FoxVK/DFMT/diploma/figures/breadborad-landscape.jpg

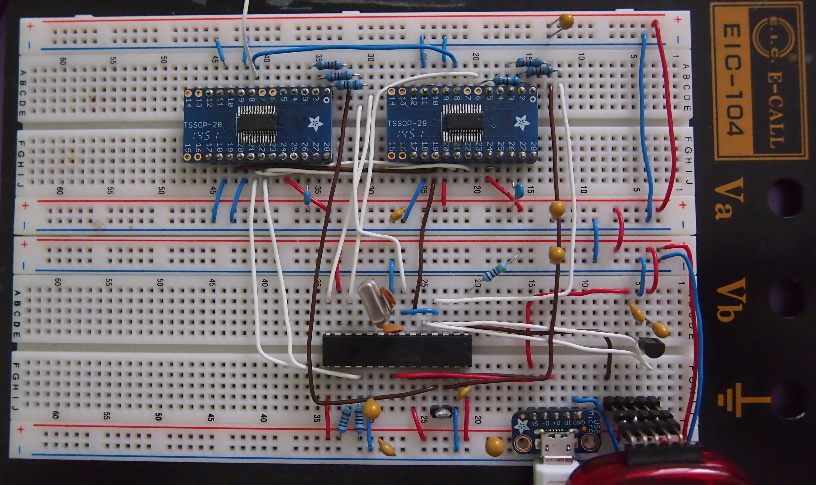
diploma/figures/breadborad-landscape.jpg
