FoxVK/DFMT/diploma/figures/breadborad-portrait.jpg

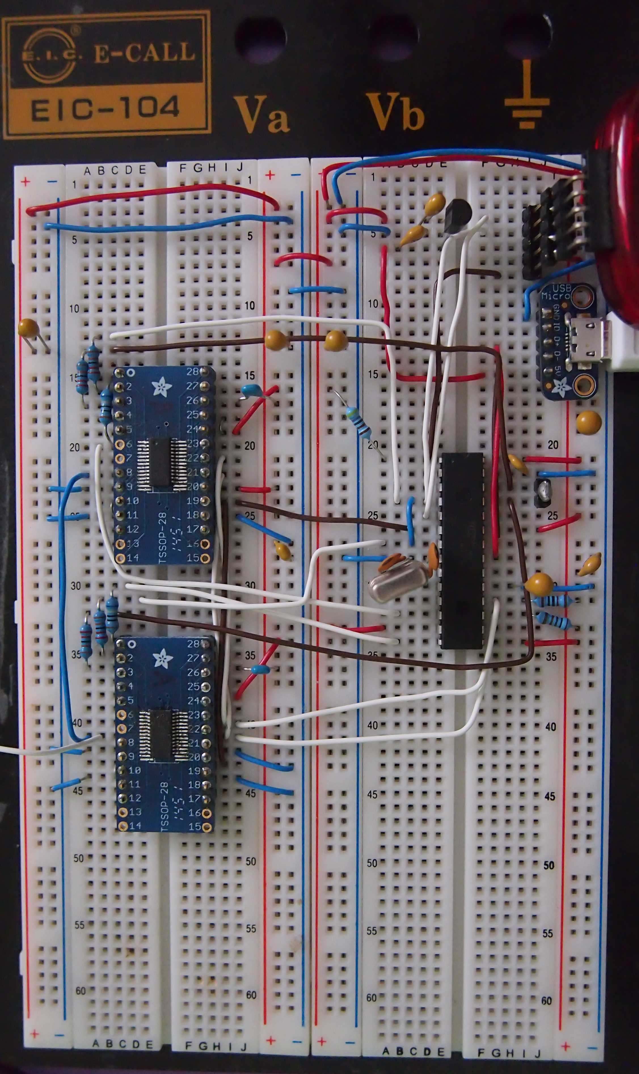
diploma/figures/breadborad-portrait.jpg
