FoxVK/DFMT/diploma/figures/dfmt-win-no-drv.png

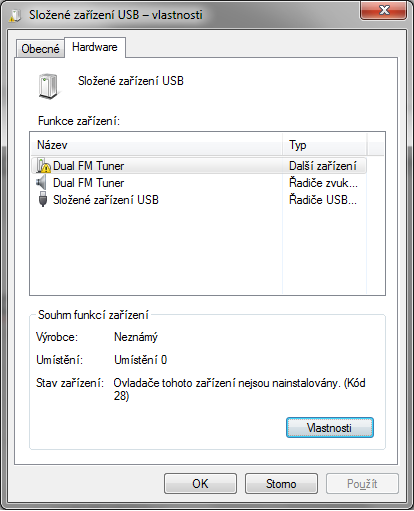
diploma/figures/dfmt-win-no-drv.png
