FoxVK/DFMT/diploma/figures/gui.png

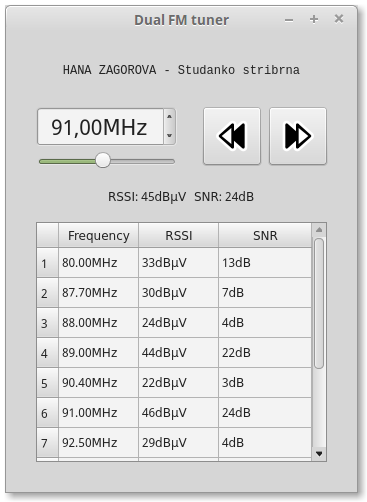
diploma/figures/gui.png
