FoxVK/DFMT/diploma/figures/i2s_format.png

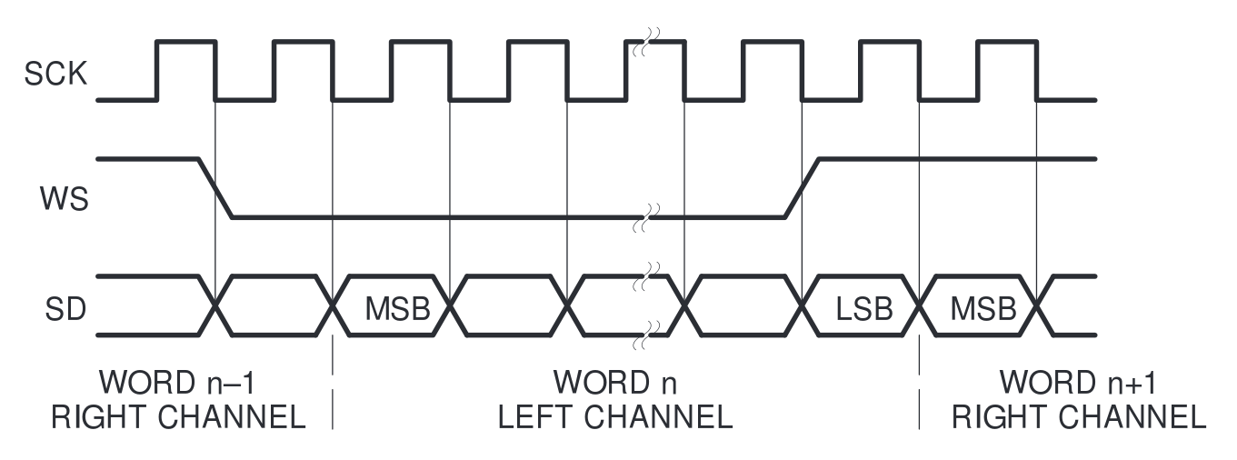
diploma/figures/i2s_format.png
