FoxVK/DFMT/diploma/figures/prohlaseni.jpg

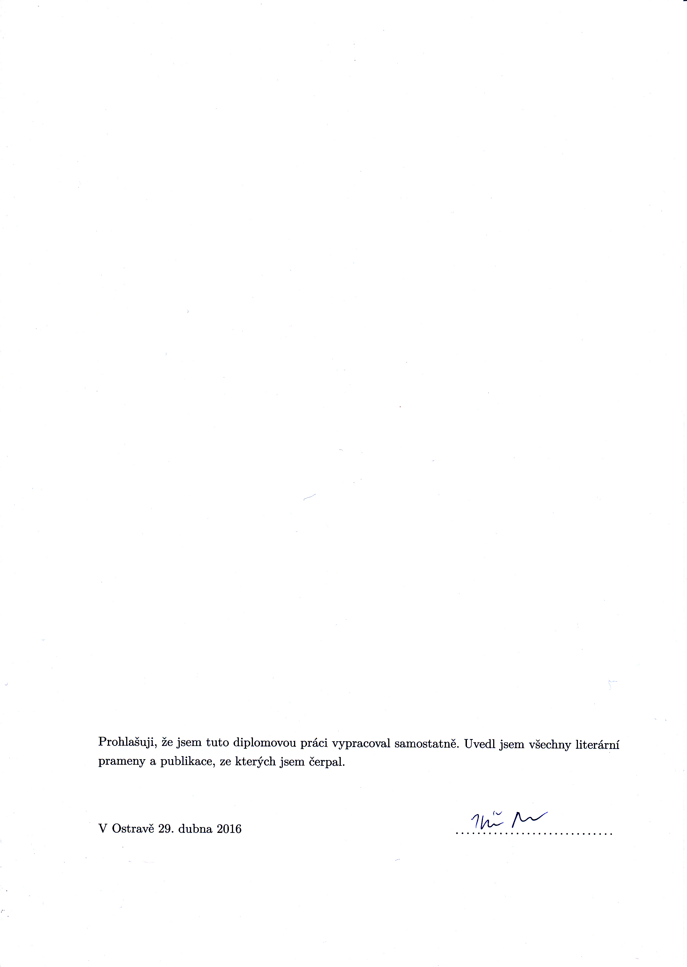
diploma/figures/prohlaseni.jpg
