FoxVK/DFMT/diploma/figures/usb-bdt-hwsw.png

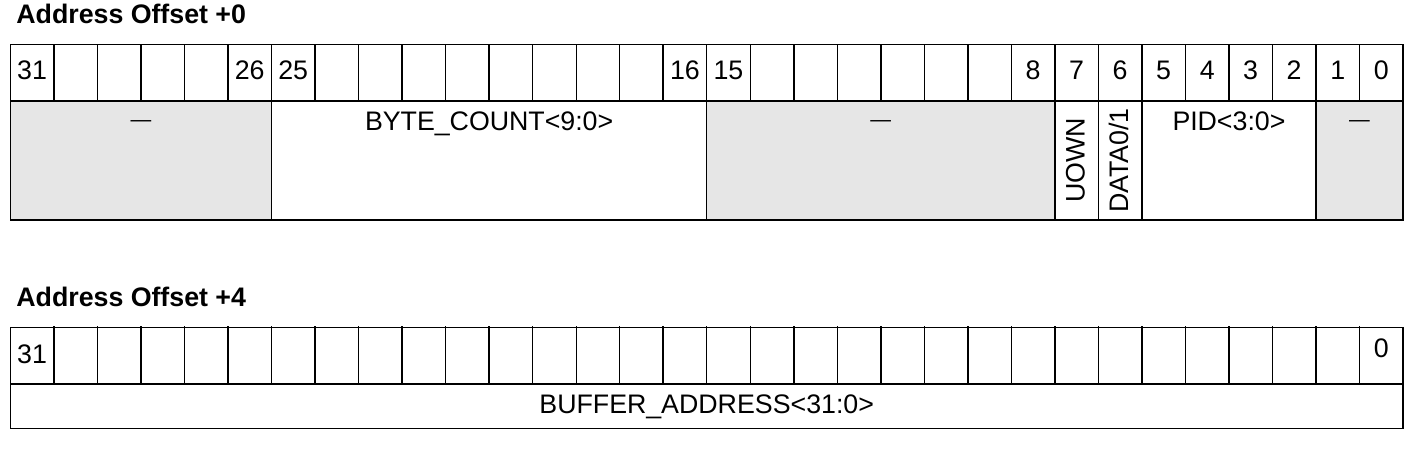
diploma/figures/usb-bdt-hwsw.png
