FoxVK/DFMT/diploma/figures/usb-bdt-swhw.png

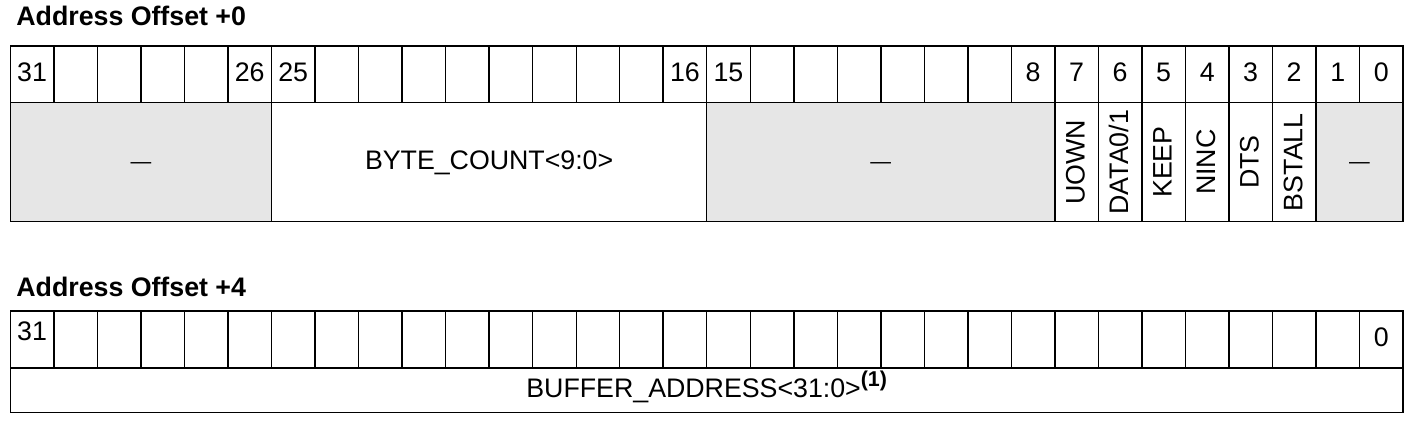
diploma/figures/usb-bdt-swhw.png
