FoxVK/DFMT/media/boardV1-botom.jpg

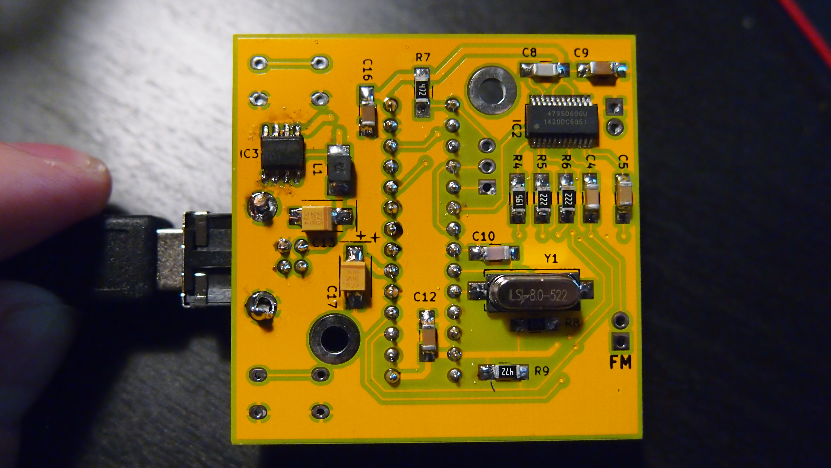
media/boardV1-botom.jpg
