FoxVK/DFMT/media/gui.png

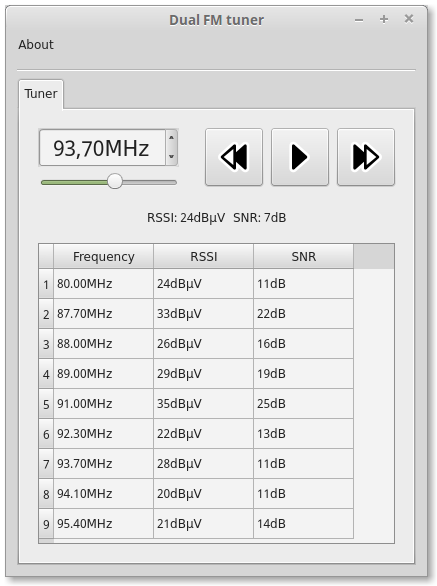
media/gui.png
