FoxVK/DFMT/firmware/tuner_audio.c

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
    Copyright: Pavel Kovar 2015 <pavel.kovar@vsetin.org>.
 */
// </editor-fold>

#include <xc.h>
#include "drv/utils.h"
#include "tuner_audio.h"
#include "drv/debug_uart.h"


static struct{
    Queue free, filled;
    void *qbuf_free[AUDIO_PACKET_BUFS], *qbuf_filled[AUDIO_PACKET_BUFS];
    AudioFrame  frame_buf[AUDIO_PACKET_BUFS];
}aud_data[2];

static struct SampleRateCorrection{
    enum {SR_COR_OFF, SR_COR_FIRST_RUN, SR_COR_ON} state;  ///< OFF = suspended
    int direciton;   ///<  +1 one more or -1 one less
    unsigned cor_rate;  ///<How often
    unsigned cor_cntr;
    int last_dif;  ///< tuner packet - usb sofs from last time
    
    int tuner_samples;
    int usb_sofs;
}sr_cor;

static volatile unsigned int *DCHxDSA[] = {&DCH0DSA, &DCH1DSA, &DCH2DSA, &DCH3DSA};
static volatile unsigned int *DCHxDSIZ[] = {&DCH0DSIZ, &DCH1DSIZ, &DCH2DSIZ, &DCH3DSIZ};    
static volatile __DCH0CONbits_t *DCHxCONbits[] = {&DCH0CONbits, 
                                    (__DCH0CONbits_t*)&DCH1CONbits, 
                                    (__DCH0CONbits_t*)&DCH2CONbits, 
                                    (__DCH0CONbits_t*)&DCH3CONbits};
static volatile __DCH0INTbits_t *DCHxINTbits[] = {&DCH0INTbits, 
                                    (__DCH0INTbits_t*)&DCH1INTbits, 
                                    (__DCH0INTbits_t*)&DCH2INTbits, 
                                    (__DCH0INTbits_t*)&DCH3INTbits};

static size_t sr_cor_packet_size(int tuner);
static void sr_cor_init();

static void arm_dma(int dma)
{
    static char *title[] = {"AD0\r\n","AD1\r\n","AD2\r\n","AD3\r\n"};
    static char *num[] = {"0 ","1 ","2 ","3 ","4 ", "5 ", "6 ", "7 ", "8 ", "9 ", "10 "};
    
    
    int tuner = (dma>1) ? 1 : 0 ;
    
    void *buf = queue_pop(&aud_data[tuner].free);
    if(!buf)
    {
        buf = queue_pop(&aud_data[tuner].filled);
    }
    if(!buf)    
        debughalt();
    size_t size = sr_cor_packet_size(tuner);  
    
    ((AudioFrame*)buf)->size = (size>(AUDIO_SAMPLE_RATE * AUDIO_SAMPLE_CHAN_BYTES * 2)) ? (AUDIO_SAMPLE_RATE * AUDIO_SAMPLE_CHAN_BYTES * 2) : size;
    
    *DCHxDSA[dma]  = virt2phy(buf);
    *DCHxDSIZ[dma] = size;
    

}

static void dma_init()
{
    DCH0SSA = DCH1SSA = virt2phy((void*)&SPI1BUF);
    DCH2SSA = DCH3SSA = virt2phy((void*)&SPI2BUF);
    
    DCH0SSIZ = DCH1SSIZ = DCH2SSIZ = DCH3SSIZ = AUDIO_SAMPLE_CHAN_BYTES;
    DCH0CSIZ = DCH1CSIZ = DCH2CSIZ = DCH3CSIZ = AUDIO_SAMPLE_CHAN_BYTES; //bytes per event
    
    DCH0DSIZ = DCH1DSIZ = DCH2DSIZ = DCH3DSIZ = sizeof(AudioFrame);
    
    DCH0CONbits.CHCHN = DCH1CONbits.CHCHN = 1;
    DCH2CONbits.CHCHN = DCH3CONbits.CHCHN = 1;
    //CHCHNS=1 Chain to channel lower in natural priority (CH1 will be enabled by CH2 transfer complete)
    DCH0CONbits.CHCHNS = DCH2CONbits.CHCHNS = 1;
    
    DCH0ECONbits.CHSIRQ = DCH1ECONbits.CHSIRQ = 37;   //cell start interrupt number 
    DCH0ECONbits.SIRQEN = DCH1ECONbits.SIRQEN = 1;    //start cell transfer when chsirq match
    
    DCH2ECONbits.CHSIRQ = DCH3ECONbits.CHSIRQ = 51;   //cell start interrupt number 
    DCH2ECONbits.SIRQEN = DCH3ECONbits.SIRQEN = 1;    //start cell transfer when chsirq match
    
    
    DCH0INT = DCH1INT = DCH2INT = DCH3INT = 0;
    
    
    int i;
    for(i=0; i<4; i++)
        arm_dma(i);    
    
    DCH0INTbits.CHDDIF = DCH1INTbits.CHDDIF = 0;
    DCH2INTbits.CHDDIF = DCH3INTbits.CHDDIF = 0;
    DCH0CONbits.CHEN = 1;
    DCH2CONbits.CHEN = 1;
}

static void i2s_init()
{
    SPI1CONbits.ON = SPI2CONbits.ON = 0;
    Nop();
    SPI1CONbits.DISSDO = SPI2CONbits.DISSDO = 1;     //disable output bit
    //SPI1CONbits.ENHBUF = 1;     //enchanced buffer enable
    SPI1CONbits.MSTEN = 1;      //enable master - we will generate clock on I2S1 not on I2S2!
    SPI1CON2bits.AUDEN = SPI2CON2bits.AUDEN = 1;     //enable audio

    SPI1CONbits.CKP = SPI2CONbits.CKP = 1;        //clock idle in low

    SPI1STATbits.SPIROV = SPI2STATbits.SPIROV = 0;    //no overflow
    
    SPI1BRG = 12;       //clock,  32bit frame X 48khz sampling = 1536kHz - now we have 1?538?461,538461538
    
    IFS1bits.SPI1RXIF = 0;
    IFS1bits.SPI2RXIF = 0;
}

void* tuner_audio_get_buf(int tuner)
{
    if (queue_count(&aud_data[tuner].filled) <= 1)
    {
        return NULL;
    }
    else
        return queue_pop(&aud_data[tuner].filled);
}

bool  tuner_audio_put_buf(int tuner, void* buf)
{
    if (queue_full(&aud_data[tuner].free))
        return false;
    else
    {
        queue_push(&aud_data[tuner].free, buf);
        return true;
    }
}



void tuner_audio_init()
{
    int i,j;
    for(i=0; i<2; i++)
    {
        queue_init(&aud_data[i].filled, aud_data[i].qbuf_filled, AUDIO_PACKET_BUFS);
        queue_init(&aud_data[i].free,   aud_data[i].qbuf_free,   AUDIO_PACKET_BUFS);
        
        for (j=0; j<AUDIO_PACKET_BUFS; j++)
            queue_push(&aud_data[i].free, &aud_data[i].frame_buf[j]);
    }
       
    dma_init();
    i2s_init();
    sr_cor_init();
    DMACONbits.ON = 1;
    SPI2CONbits.ON = 1;
    SPI1CONbits.ON = 1;
}

void tuner_audio_task()
{
    int i = 0;
    for (;i<4;i++)
    {
        if(DCHxINTbits[i]->CHDDIF)
        {
            DCHxINTbits[i]->CHDDIF = 0;
            queue_push(&aud_data[(i>1)?1:0].filled, phy2virt(*DCHxDSA[i]));
            arm_dma(i);
        }
    }
}

void tuner_audio_sof()
{
    sr_cor.usb_sofs++;
    
    if( sr_cor.state == SR_COR_FIRST_RUN && 
        sr_cor.tuner_samples > 50 &&
        sr_cor.usb_sofs > 50)
    {
        sr_cor.state = SR_COR_ON;
        sr_cor.tuner_samples = sr_cor.usb_sofs = 0;
    }
    
    if(sr_cor.usb_sofs == AUDIO_SR_SOFS_INTERVAL && sr_cor.state == SR_COR_ON)
    {
        int dif = (sr_cor.tuner_samples - sr_cor.usb_sofs) ;
        dif += sr_cor.last_dif;
        sr_cor.last_dif = dif;

        if(dif == 0)
        {
            sr_cor.direciton = 0;
        }
        else
        {            
            int rate = (AUDIO_SR_SOFS_INTERVAL / AUDIO_SAMPLE_RATE) / dif;

            if(rate < 0)
            {
                sr_cor.cor_rate = (0 - rate);
                sr_cor.direciton = -1;
            }
            else if(rate == 0)
            {
                sr_cor.direciton = 0;
                sr_cor.last_dif = 0;
            }
            else
            {
                sr_cor.cor_rate = rate;
                sr_cor.direciton = 1;
            }
        }

        sr_cor.tuner_samples = sr_cor.usb_sofs = 0;
    }
}

static size_t sr_cor_packet_size(int tuner)
{
    if(tuner==0)
    {
        if(sr_cor.state!=SR_COR_OFF)
            sr_cor.tuner_samples++;
        
        sr_cor.cor_cntr++;
        if(sr_cor.cor_cntr >= sr_cor.cor_rate)
            sr_cor.cor_cntr = 0;
    }
    
    if(sr_cor.cor_cntr != 1)
        return (AUDIO_SAMPLE_RATE * AUDIO_SAMPLE_CHAN_BYTES * 2 );
    else
        return (AUDIO_SAMPLE_RATE * AUDIO_SAMPLE_CHAN_BYTES * 2 )+ sr_cor.direciton;
}

static void sr_cor_init()
{
        sr_cor.cor_rate = 0;
        sr_cor.direciton = 0;
        sr_cor.tuner_samples = 0;
        sr_cor.usb_sofs = 0;
        sr_cor.last_dif = 0;
        sr_cor.state = SR_COR_OFF;
        sr_cor.cor_cntr = 0;
}

void tuner_audio_sr_cor_on(bool state)
{
    if(state)
    {
        //sr_cor.cor_rate = 0;
        //sr_cor.direciton = 0;
        sr_cor.tuner_samples = 0;
        sr_cor.usb_sofs = 0;
        sr_cor.state = SR_COR_FIRST_RUN;
    }
    else
    {
        sr_cor.state = SR_COR_OFF;
    }
}
