FoxVK/DFMT/firmware/app.c

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
    Copyright: Pavel Kovar 2015 <pavel.kovar@vsetin.org>.
 */
// </editor-fold>

#include "app.h"
#include "drv/debug_uart.h"
#include "drv/utils.h"
#include "drv/usb.h"
#include "drv/usb_audio.h"
#include "tuner_audio.h"
#include "tuner_control.h"
#include "tuner_com.h"
#include "tunnel.h"

extern Usb_config config;

static Usb_audio_iface *audio_if;

void usb_event(Usb_event ev)
{
    switch(ev)
    {
        case USB_EV_CONFIGURED:
        {
            static char* line = "configured\r\n";
            debug_uart_write(line);
            
            if(usb_current_config() == 1)
                usb_audio_claim(audio_if);
            else
                usb_audio_release(audio_if);
            
            tunnel_reset_data01();
            tuner_audio_sr_cor_on(true);
        }
            break;
        case USB_EV_RESET:
        {
            static char* line = "usb reset\r\n";
            debug_uart_write(line);
            tuner_audio_sr_cor_on(false);
        }
            break;
        case USB_EV_SUSPENDED:
        {
            static char* line = "suspended\r\n";
            debug_uart_write(line);
        }
            break;
        case USB_EV_RESUMED:
        {
            static char* line = "RESUMED\r\n";
            debug_uart_write(line);
            tuner_audio_sr_cor_on(true);
        }
            break;
        case USB_EV_SOF:
        {
            tuner_audio_sof();
        }
            break;
        default:
            break;
    }
}

bool app_usb_ct_handler(Usb_ct_request *rq)
{
    return usb_audio_ct_handler(audio_if, rq);
}

void app_usb_audio_td0_handler(void * data, size_t len, void * usr_ptr)
{
    (void) len;
    (void) usr_ptr;
    
    tuner_audio_put_buf(0, data);
}

inline void app_init()
{
    debug_uart_init();
    static char * run = "\n\rReseted\n\r";
    debug_uart_write(run);
    
    tuner_init();
    tuner_audio_init();
    tuner_control_pwr(true);

    config.event_callback = usb_event;
    config.ct_request_callback = &app_usb_ct_handler;
    usb_init(&config);

    static Usb_audio_iface uai;
    audio_if = &uai;
    usb_audio_init(audio_if, 1, NULL);
    Usb_audio_add_ep(audio_if, USB_EP01, USB_EP_IN, app_usb_audio_td0_handler);   
    
    tunnel_init();
    
    static char *initd = "init done\n\r";  
    debug_uart_write(initd);
}

inline void app_task()
{    
    debug_uart_task();
    usb_task();
    tuner_audio_task();
    tuner_control_task();
    tunnel_task();
    
    
    if(usb_audio_can_play(audio_if))
    {
        static AudioFrame *to_send = NULL;
        
        if(to_send == NULL)
            to_send = tuner_audio_get_buf(0);
    
        if(to_send)
        { 
            if(Usb_audio_send(audio_if, USB_EP01, to_send, to_send->size)==USB_RW_REQ_OK)
            {
                //debughalt();
                to_send = NULL;
            }
        }
    }
}
