FoxVK/DFMT/firmware/drv/utils.c

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
    Copyright: Pavel Kovar 2015 <pavel.kovar@vsetin.org>.
 */
// </editor-fold>

#include "utils.h"

void uint2hex(unsigned number, char* buf, size_t length)
{
    int i;
    const int digits = sizeof(unsigned);

    buf += length-1;

    for(i=0;i<length; i++)
    {
        const int remain = digits - i;
        if(remain>0)
        {
            char digit = number & 0xf;
            *buf = (digit > 9) ? digit+'A'-10 : digit+'0';
            number >>= 4;
        }
        else if (remain == 0)
            *buf = 'x';
        else if (remain == -1)
            *buf = '0';
        else
            *buf = ' ';
        buf--;
    }
}


unsigned virt2phy(void* virt_addr)
{
    return ((unsigned)virt_addr) & 0x1FFFFFFF;
}

void* phy2virt(unsigned phy_addr)
{
    phy_addr |= 0xA0000000;

    union{
        unsigned phy;
        void * virt;
    }addr;

    addr.phy = phy_addr;

    return addr.virt;
}




void queue_init(Queue *queue, void **array, size_t size)
{
    //size is count of void* in array. For example: if *void[10] then size=10. Not size=sizeof(array);
    queue->array = array;
    queue->size  = size;

    queue->head  = 0;
    queue->tail  = 0;
    queue->count = 0;
}

bool queue_full(Queue *queue)
{
    return (queue->count >= queue->size) ? true : false;
}

bool queue_empty(Queue *queue)
{
    return (queue->count <= 0) ? true : false;
}

int   queue_count(Queue *queue)
{
    return queue->count;
}

bool queue_push(Queue* queue, void* data_ptr)
{
    if(queue_full(queue))
        return false;

    queue->count++;

    queue->tail++;
    if(queue->tail >= queue->size)
        queue->tail = 0;
    queue->array[queue->tail] = data_ptr;

    return true;
}

void* queue_pop(Queue* queue)
{
    if(queue_empty(queue))
        return NULL;

    queue->count--;

    queue->head++;
    if(queue->head >= queue->size)
        queue->head = 0;

    return queue->array[queue->head];
}
